simonhauck/M-AI-SmartCars/doc/imgs/car_wiriring_plan.jpeg

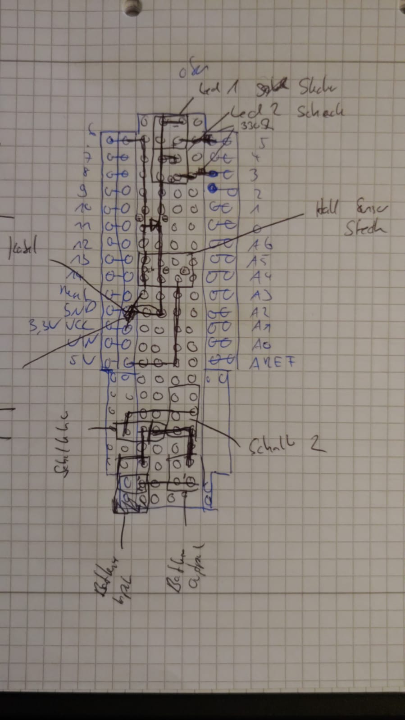
doc/imgs/car_wiriring_plan.jpeg
