simonhauck/M-AI-SmartCars/doc/imgs/finished_prototype.jpg

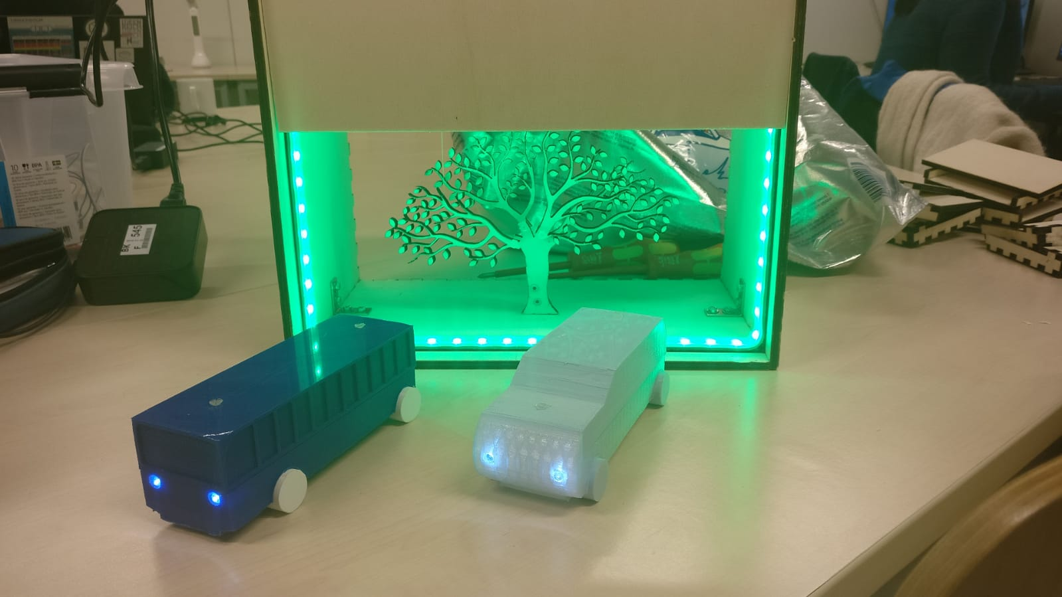
doc/imgs/finished_prototype.jpg
