simonhauck/M-AI-SmartCars/doc/imgs/sponge_prototype.jpeg

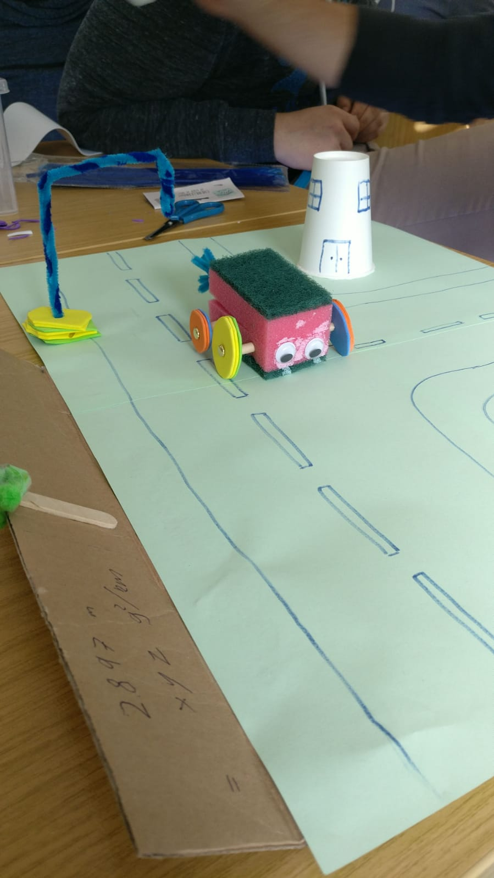
doc/imgs/sponge_prototype.jpeg
