simonhauck/M-AI-SmartCars/doc/imgs/tree_front.jpg

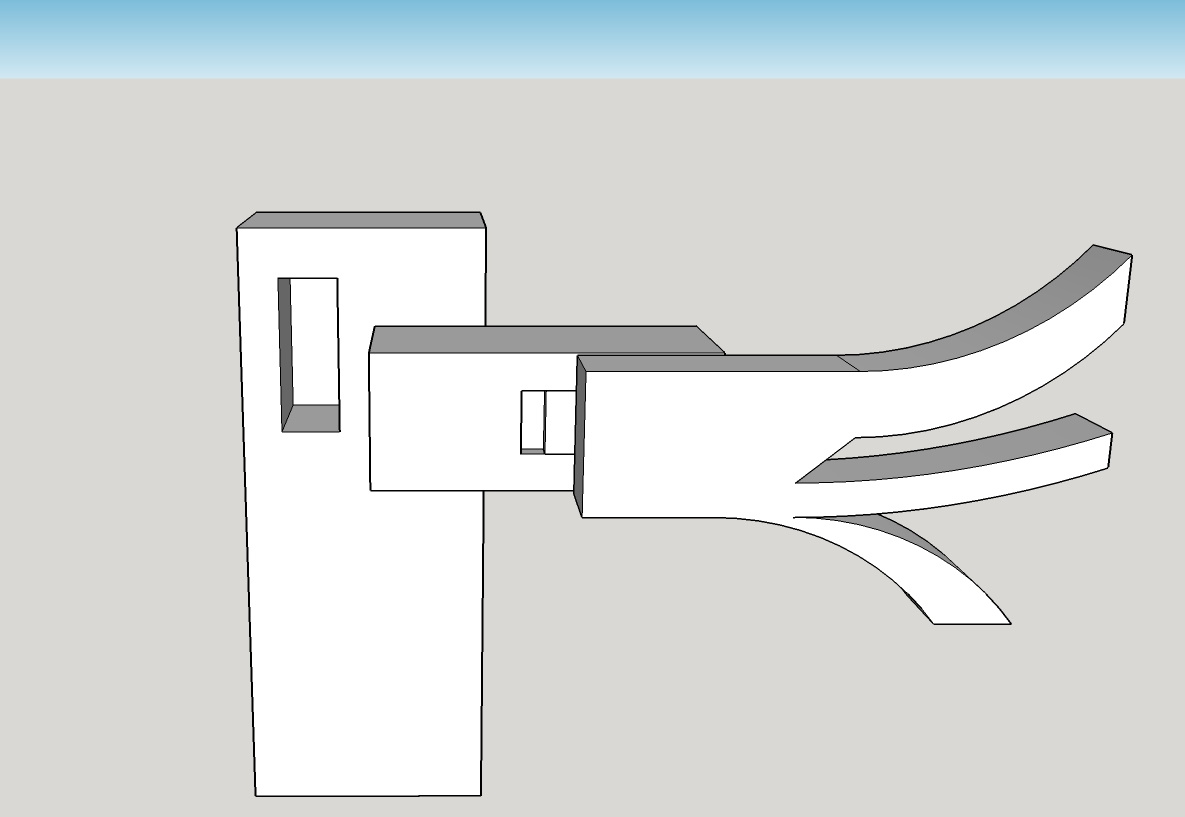
doc/imgs/tree_front.jpg
