simonhauck/M-AI-SmartCars/doc/imgs/tree_half_red.PNG

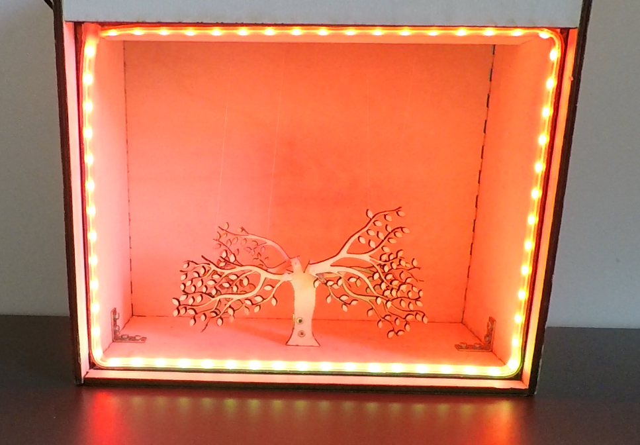
doc/imgs/tree_half_red.PNG
