simonhauck/M-AI-SmartCars/doc/imgs/tree_wiriring_iteration3.PNG

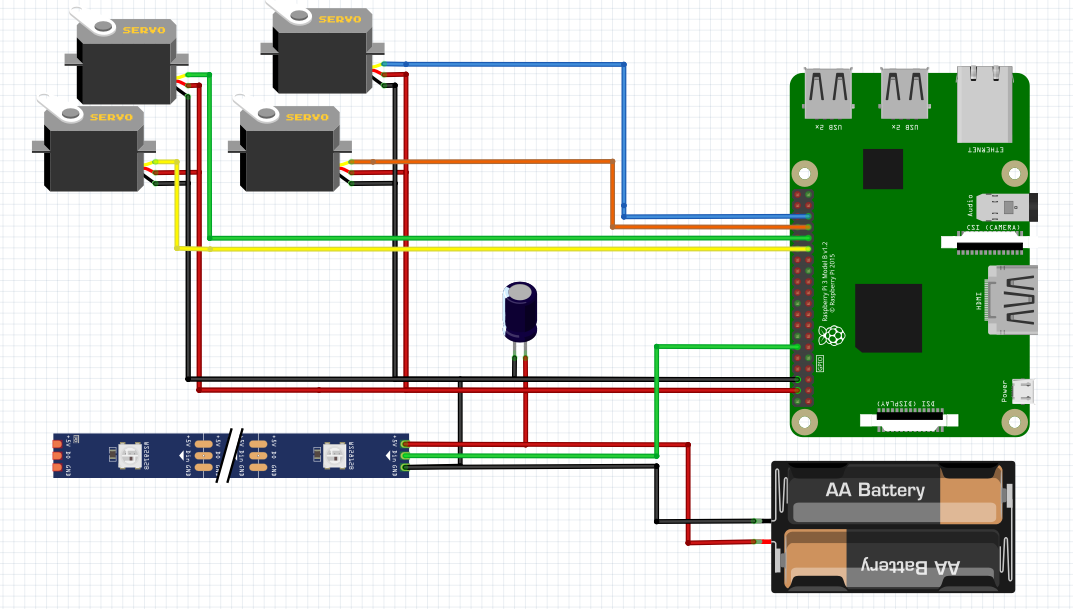
doc/imgs/tree_wiriring_iteration3.PNG
