simonhauck/M-AI-SmartCars/workshops/2019_10_09/img/slidesBackground.jpg

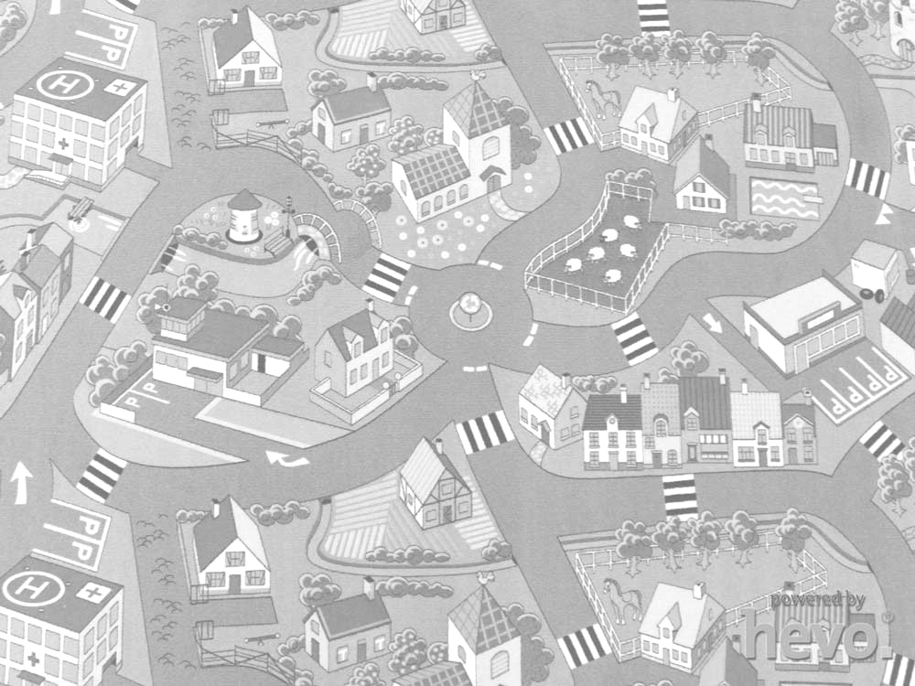
workshops/2019_10_09/img/slidesBackground.jpg
