simonhauck/M-AI-SmartCars/workshops/2019_10_09/img/WhatsApp Image 2019-10-02 at 12.51.36.jpeg

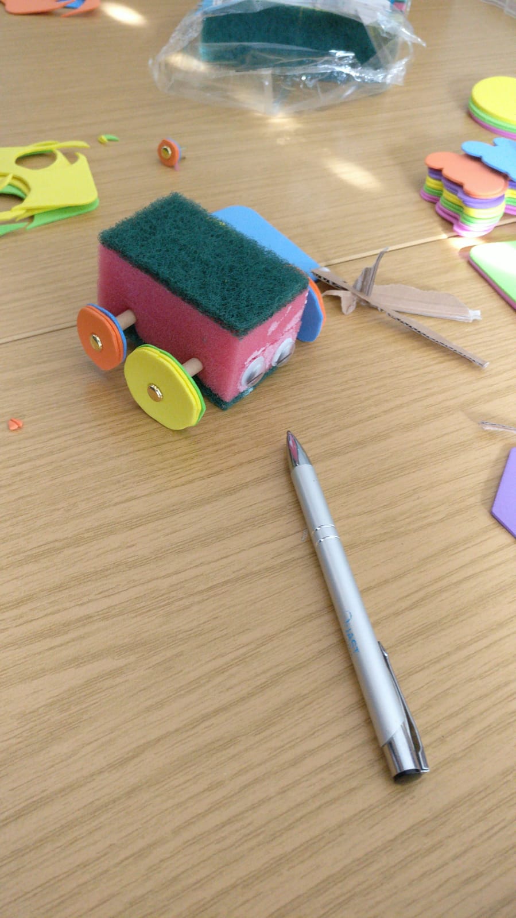
workshops/2019_10_09/img/WhatsApp Image 2019-10-02 at 12.51.36.jpeg
