simonhauck/M-AI-SmartCars/workshops/2019_10_09/img/WhatsApp Image 2019-10-02 at 13.05.25.jpeg

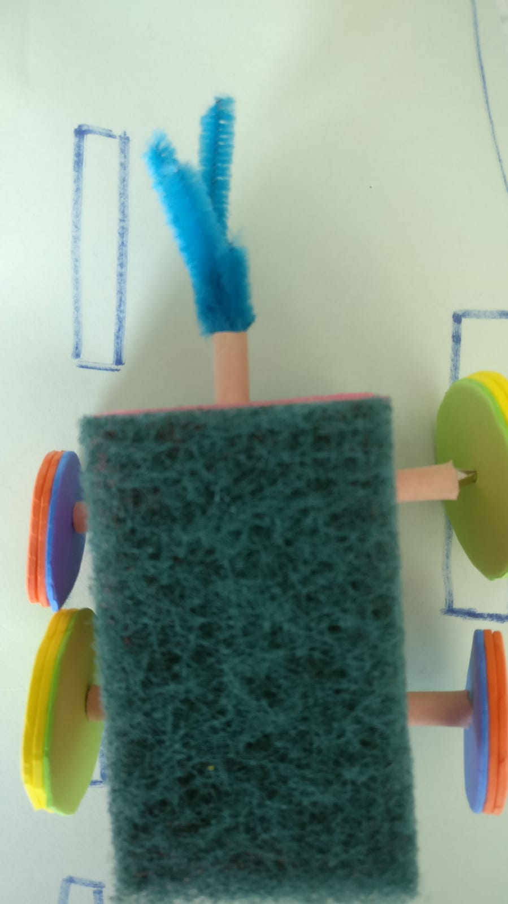
workshops/2019_10_09/img/WhatsApp Image 2019-10-02 at 13.05.25.jpeg
