simonhauck/M-AI-SmartCars/workshops/2019_10_09/img/WhatsApp Image 2019-10-06 at 16.01.23.jpeg

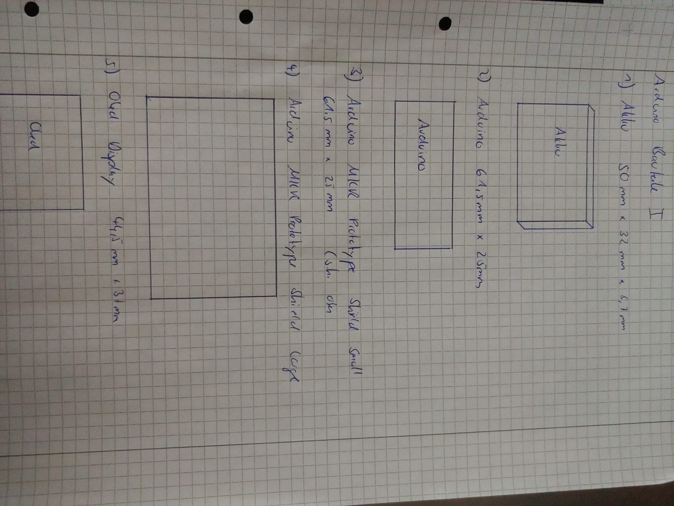
workshops/2019_10_09/img/WhatsApp Image 2019-10-06 at 16.01.23.jpeg
