simonhauck/M-AI-SmartCars/workshops/2019_10_09/img/WhatsApp Image 2019-10-08 at 15.01.02(1).jpeg

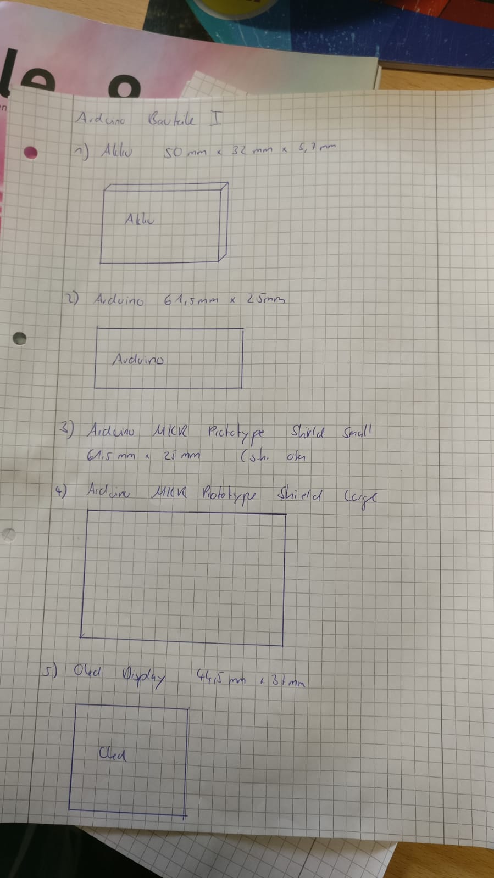
workshops/2019_10_09/img/WhatsApp Image 2019-10-08 at 15.01.02(1).jpeg
