simonhauck/M-AI-SmartCars/workshops/2019_10_23/img/car_wheel.jpg

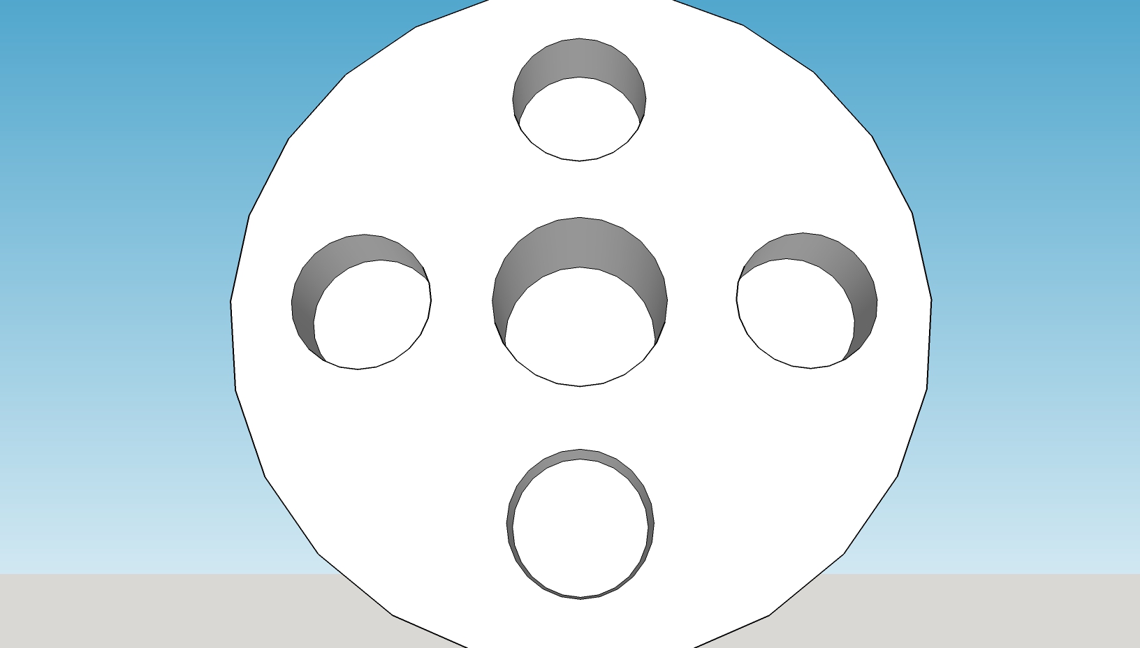
workshops/2019_10_23/img/car_wheel.jpg
