simonhauck/M-AI-SmartCars/workshops/2019_10_23/img/IMG-20191022-WA0002.jpg

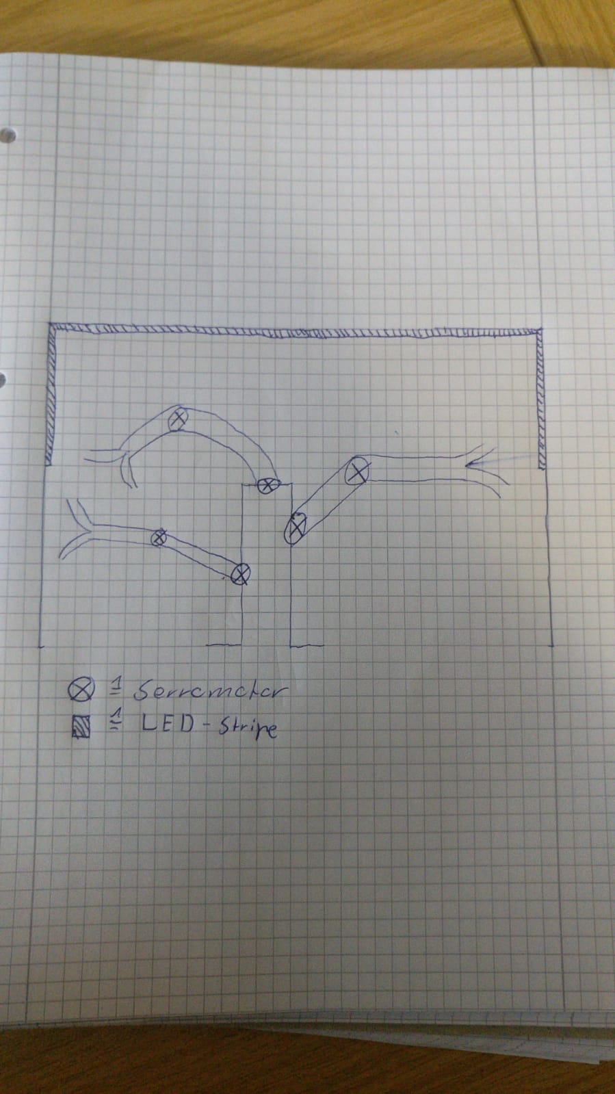
workshops/2019_10_23/img/IMG-20191022-WA0002.jpg
