simonhauck/M-AI-SmartCars/workshops/2019_11-25/img/box_v1.jpeg

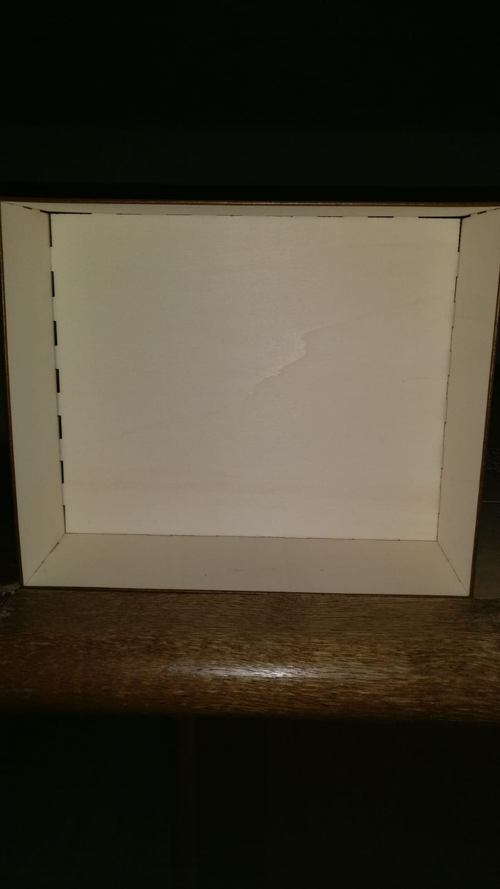
workshops/2019_11-25/img/box_v1.jpeg
