simonhauck/M-AI-SmartCars/workshops/2019_11-25/img/tree_in_box.jpeg

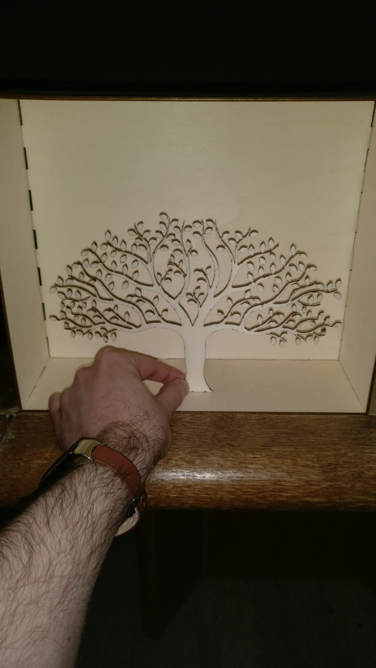
workshops/2019_11-25/img/tree_in_box.jpeg
