simonhauck/M-AI-SmartCars/workshops/2019_11-25/img/tree_v1 (2).jpeg

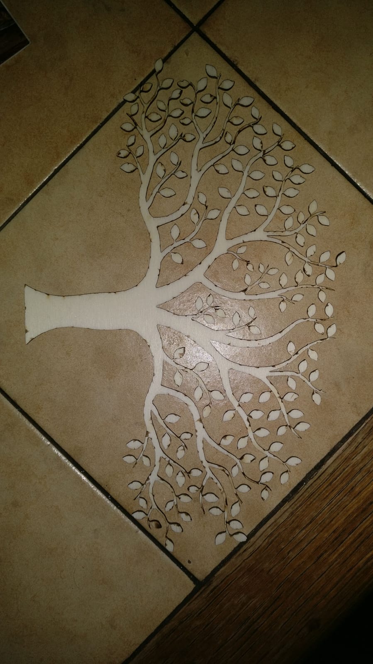
workshops/2019_11-25/img/tree_v1 (2).jpeg
