simonhauck/M-AI-SmartCars/src/3d/raw/stl/fastening_back_left2right.stl

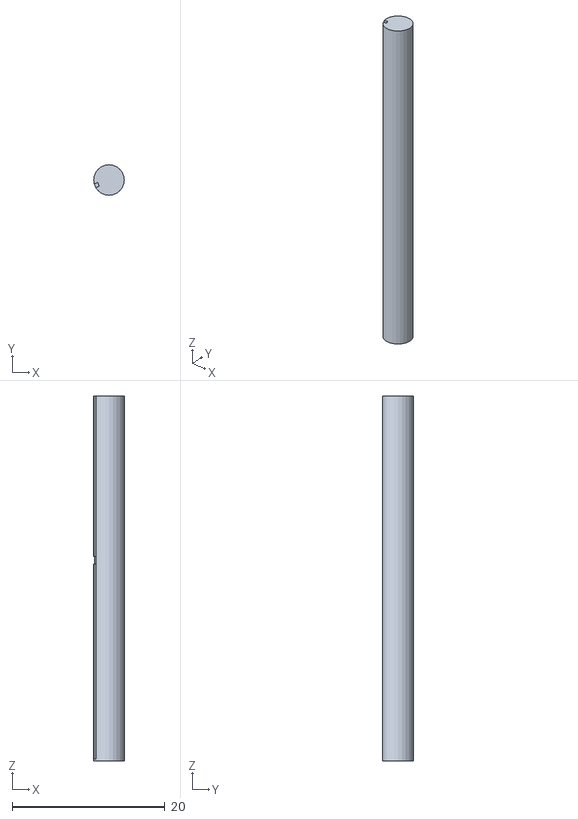
[picture p70: CAD file, 2019-11-18]
src/3d/raw/stl/fastening_back_left2right.stl
4.00 x 4.00 x 47.7
